eleven5150/temperature-meter/docs/drawings/device/Research Stand.pdf

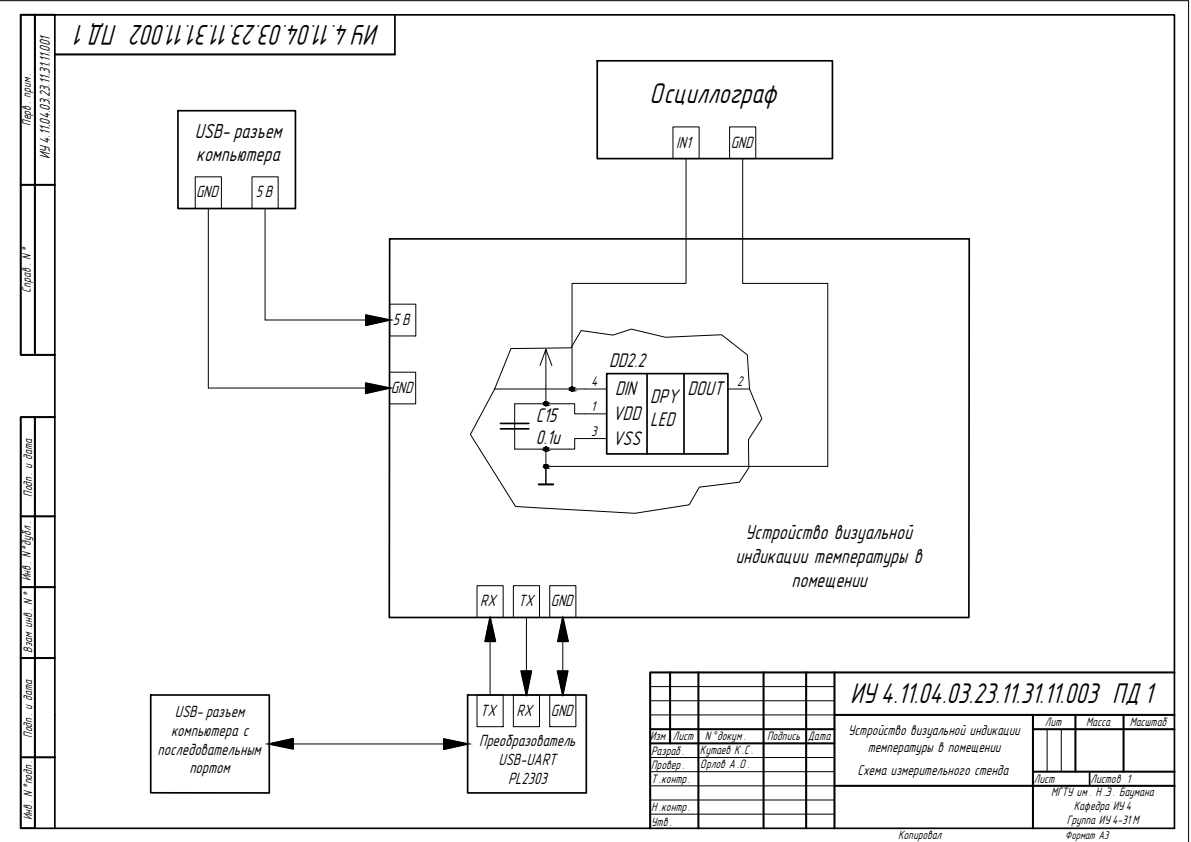
[picture p30: page 1]
Копировал; Формат А3; N °докум .; Подпись; Дата; Изм . Лист; Кутаев К .С . Орлов А .О .; МГТУ им . Н .Э . Баумана; Схема измерительного стенда Подп . и дата Инв . N °дубл . Подп . и дата Взам .инв . N ° Инв . N °подп . Перв . прим . Справ . N °; USB- разъем; GND; компьютера с; DOUT DPY; VSS 3; Устройство визуальной индикации температуры в

Устройство визуальной индикации температуры в помещении | Лит | Масса | Масштаб

Провер . Т .контр . Разраб .

Лист | Листов 1

Утв . Н .контр .

Кафедра ИУ 4 Группа ИУ 4-31 М
