eleven5150/temperature-meter/docs/drawings/cell/src/pcb_src/pcb.pdf

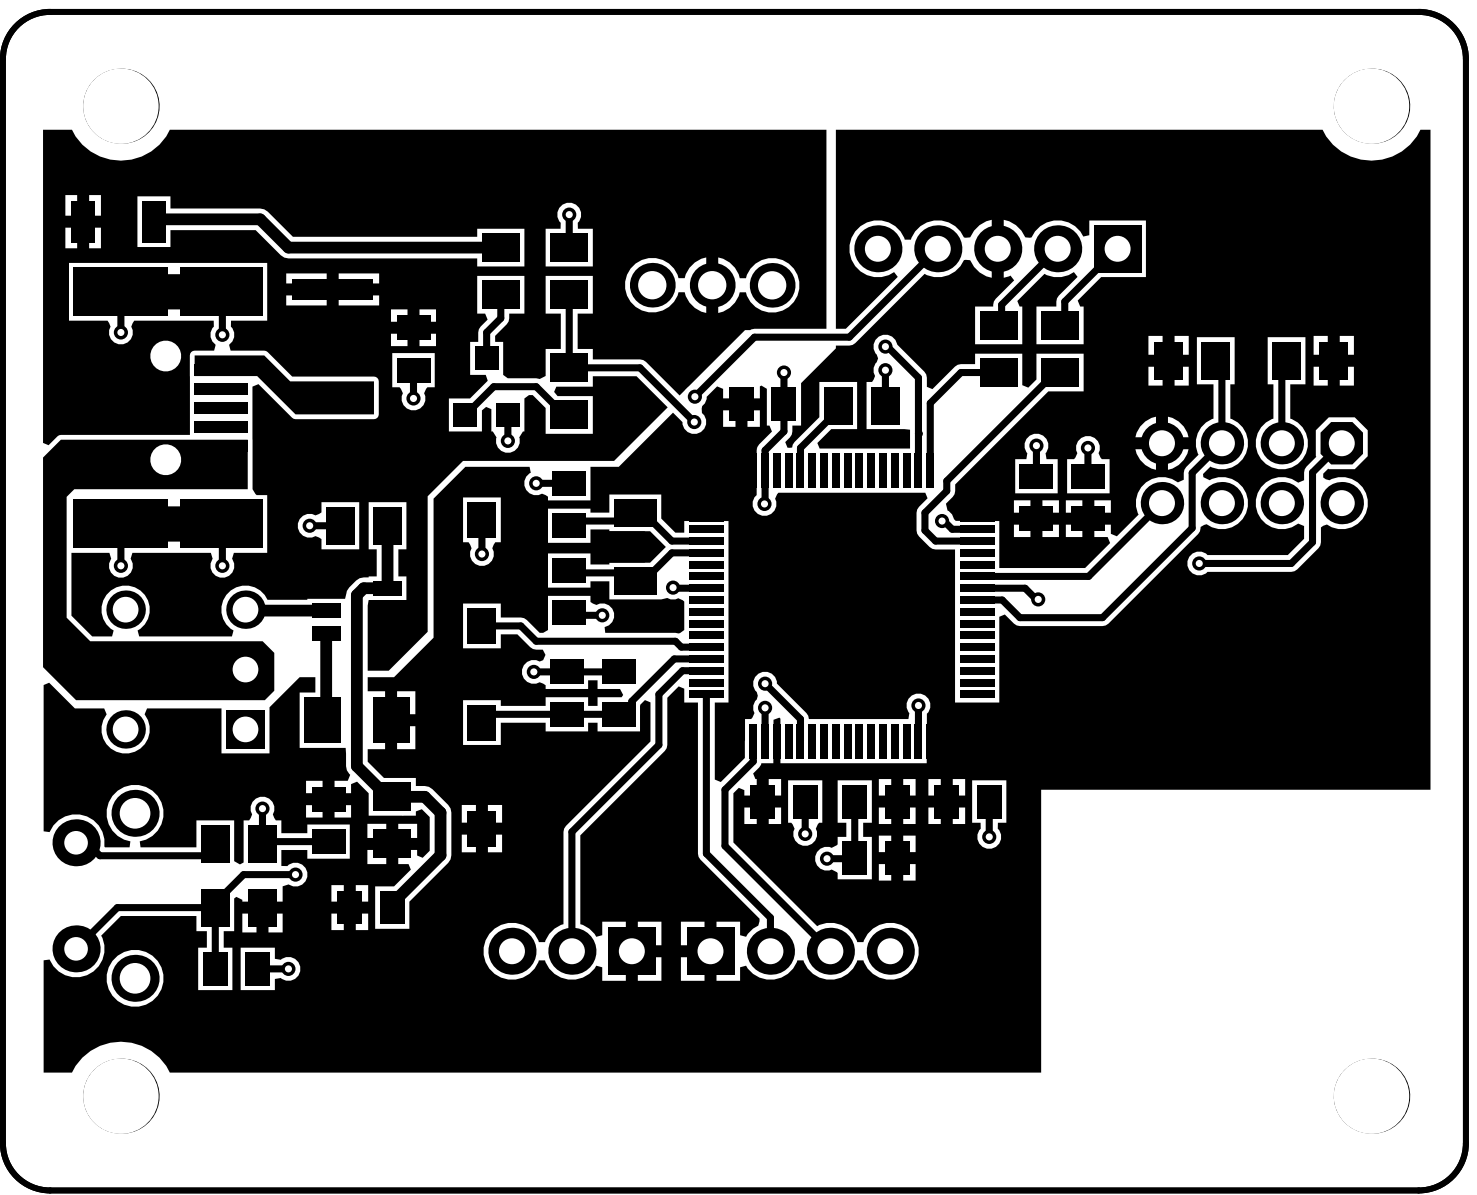
[picture p31: page 1]

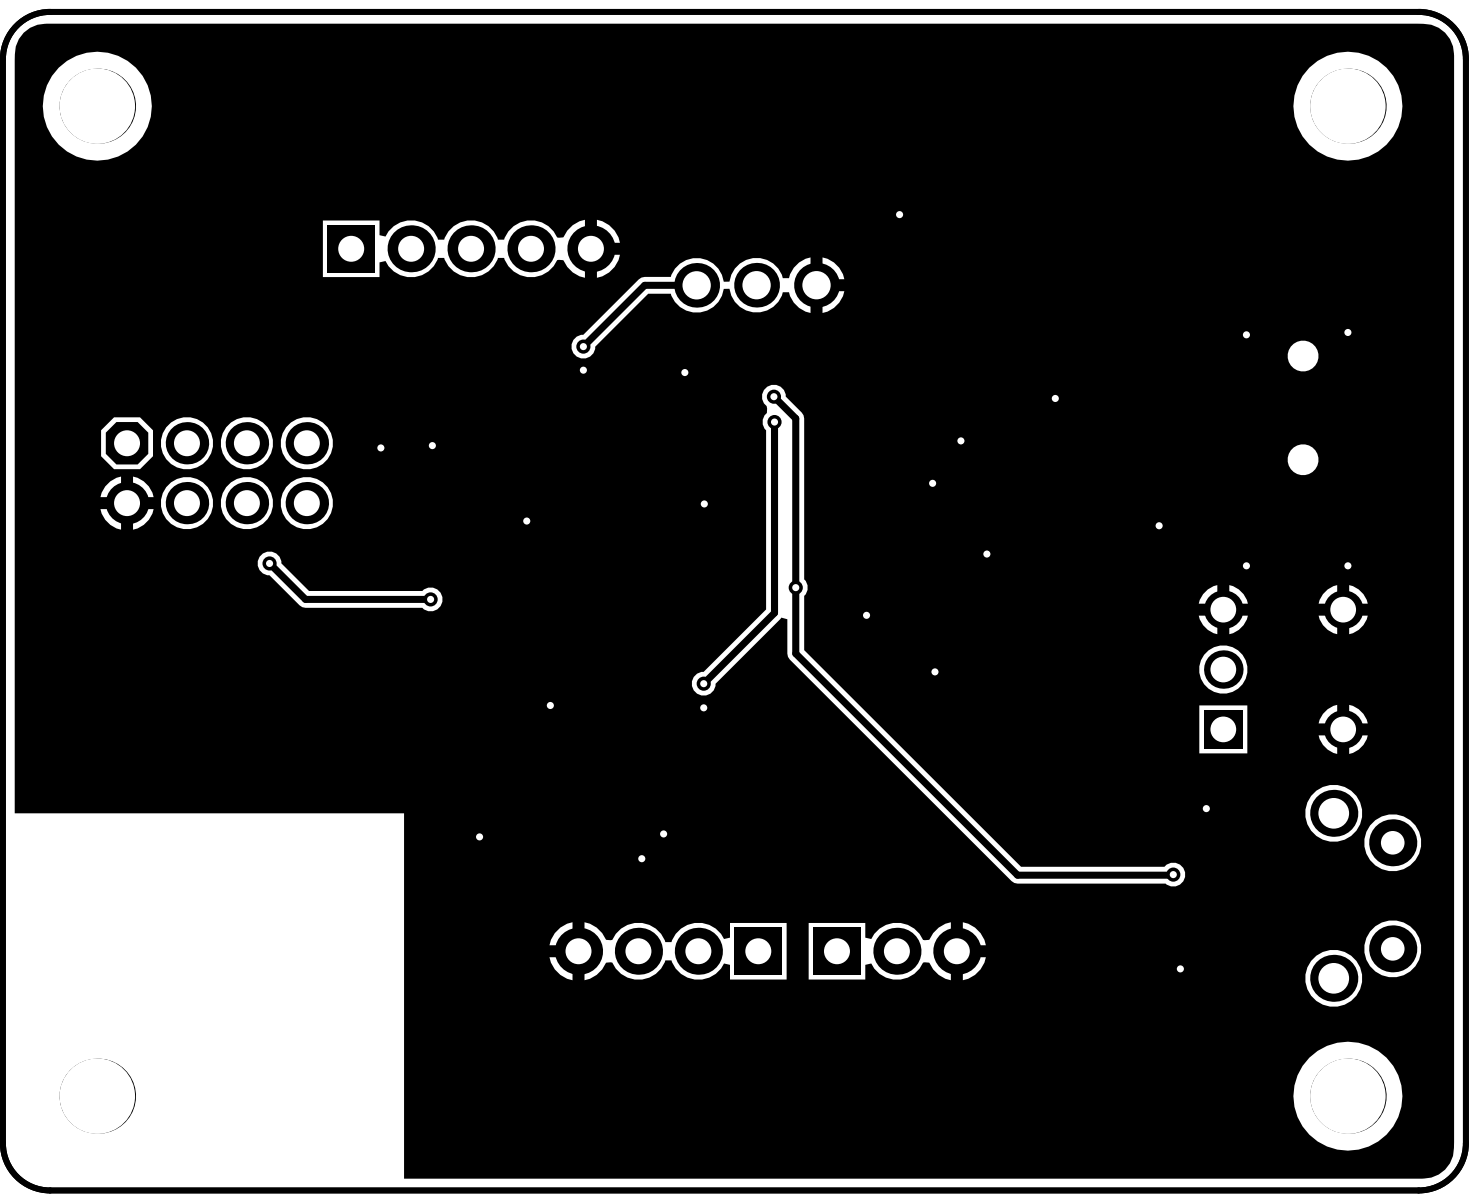
[picture p32: page 2]
